BMTEJ/CameraSenseHapticWearable/PCB/JanusSchematic/JanusSchematic.kicad_sch

## KiCad design PCB/JanusSchematic/JanusSchematic.kicad_sch (2025-03-18)

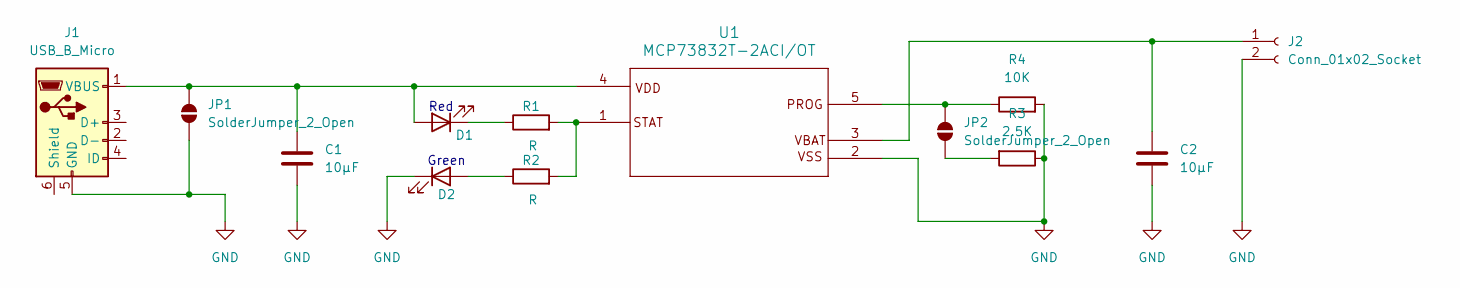
[picture p5: schematic JanusSchematic.kicad_sch]

Parts:
C1, C2: 10μF
D1, D2: LED
J1: USB_B_Micro
J2: Conn_01x02_Socket
JP1, JP2: SolderJumper_2_Open
R1, R2: R
R3: 2.5K
R4: 10K
U1: MCP73832T-2ACI/OT; SOT-23-5_MC_MCH

Connections:
GND: C1.2, C2.2, D2.1 (K), J1.5 (GND), J2.2, JP1.1 (A), R3.1, R4.2, U1.2
unnamed: C1.1, D1.2 (A), J1.1 (VBUS), JP1.2 (B), U1.4
unnamed: C2.1, J2.1, U1.3
unnamed: D1.1 (K), R1.1
unnamed: D2.2 (A), R2.1
unnamed: JP2.1 (A), R3.2
unnamed: JP2.2 (B), R4.1, U1.5
unnamed: R1.2, R2.2, U1.1

Notes on the sheet:
Green
Red
