BMTEJ/CameraSenseHapticWearable/PCB/LRA/LRAdriver/LRAdriver.kicad_sch

## KiCad design PCB/LRA/LRAdriver/LRAdriver.kicad_sch (2025-03-20)

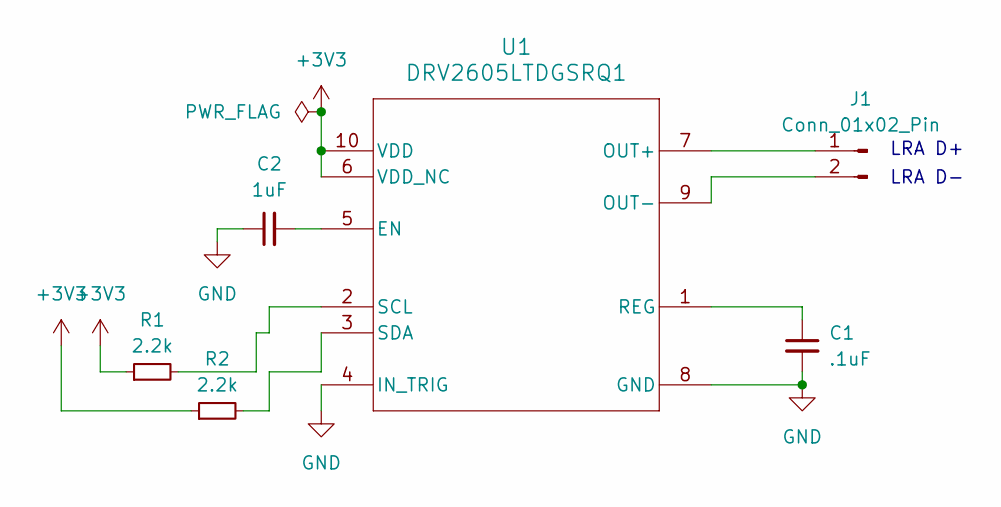
[picture p6: schematic LRAdriver.kicad_sch]

Parts:
C1: .1uF
C2: 1uF
J1: Conn_01x02_Pin
R1, R2: 2.2k
U1: DRV2605LTDGSRQ1; DGS0010A_N

Connections:
+3V3: R1.1, R2.1, U1.6 (VDD_NC), U1.10 (VDD)
GND: C1.2, C2.1, U1.4 (IN_TRIG), U1.8 (GND)
unnamed: C1.1, U1.1 (REG)
unnamed: C2.2, U1.5 (EN)
unnamed: J1.1, U1.7 (OUT+)
unnamed: J1.2, U1.9 (OUT-)
unnamed: R1.2, U1.2 (SCL)
unnamed: R2.2, U1.3 (SDA)

Notes on the sheet:
LRA D-
LRA D+
